lucabaldesi/Xilinx_cases/zc706_corners/corner-1-3.stl

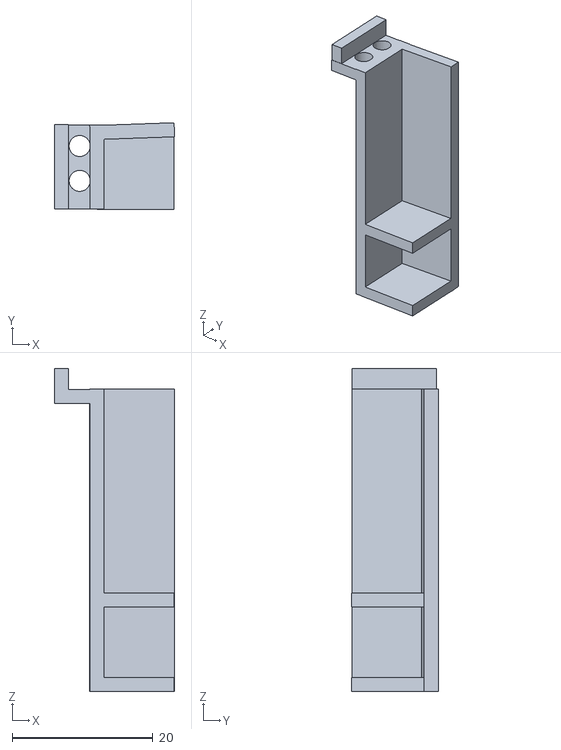
[picture p14: CAD file, 2022-02-22]
zc706_corners/corner-1-3.stl
17.1 x 12.3 x 45.9
