lucabaldesi/Xilinx_cases/zc706_corners/corner-1-4.stl

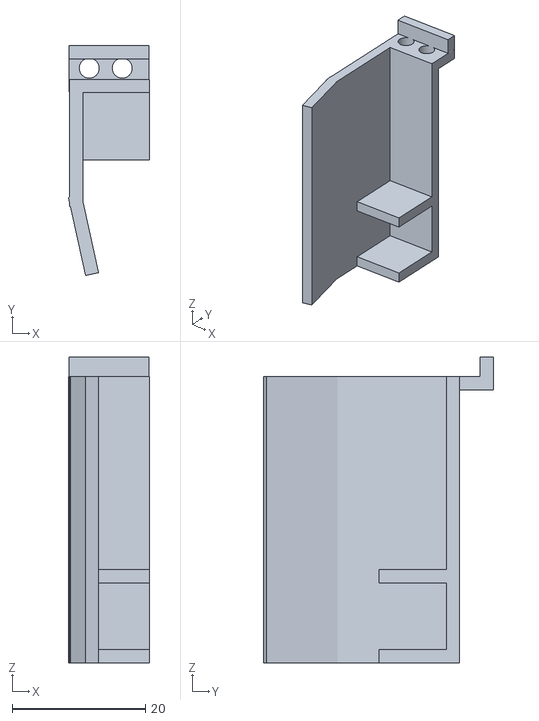
[picture p15: CAD file, 2022-02-22]
zc706_corners/corner-1-4.stl
12.2 x 34.5 x 45.9
