lucabaldesi/Xilinx_cases/zc706_corners/top_pane.dxf

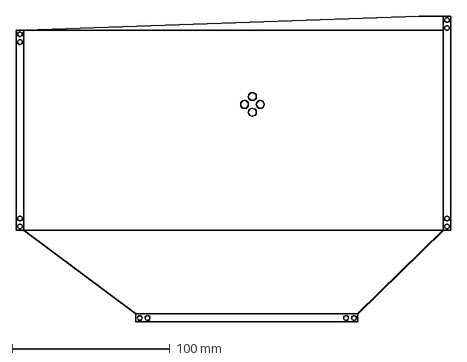
[picture p16: CAD file, 2022-02-22]
zc706_corners/top_pane.dxf
276.0 x 194.0 mm
